ddv2005/AirsoftTracker/data/at.png

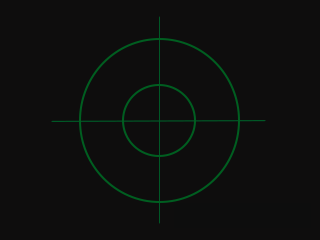
data/at.png
