ddv2005/AirsoftTracker/docs/1.jpg

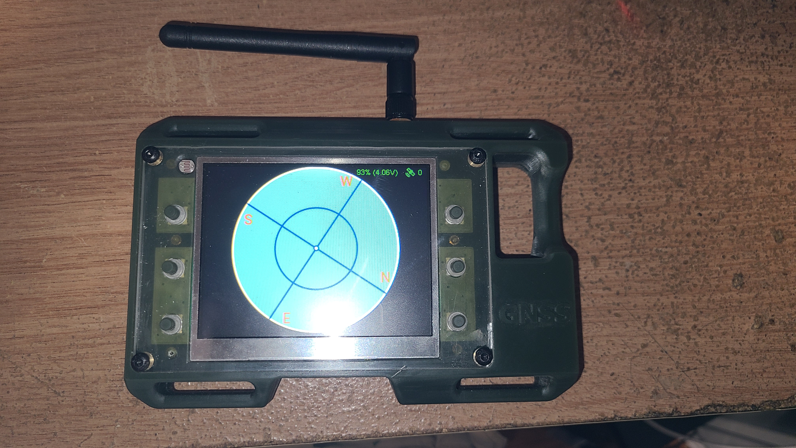
docs/1.jpg
