ddv2005/AirsoftTracker/docs/2.jpg

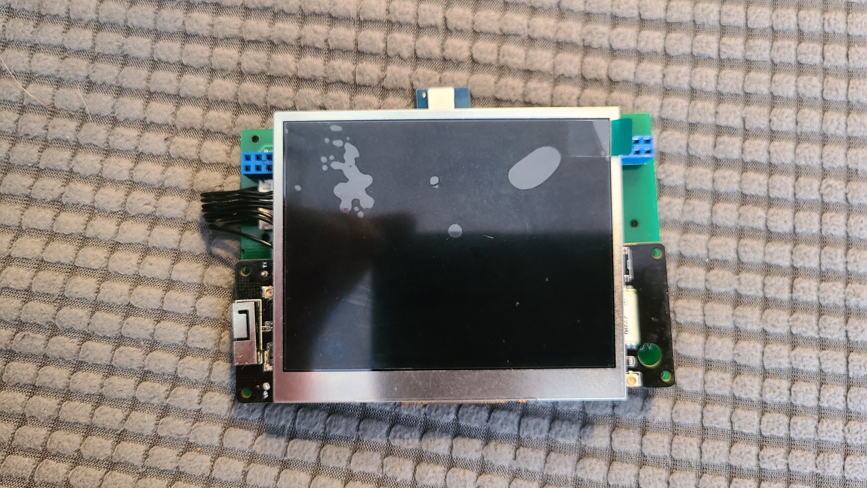
docs/2.jpg
