ddv2005/AirsoftTracker/docs/3.jpg

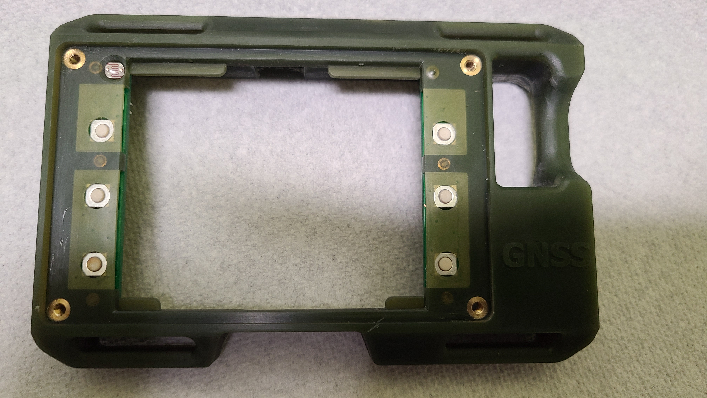
docs/3.jpg
