ddv2005/AirsoftTracker/docs/4.jpg

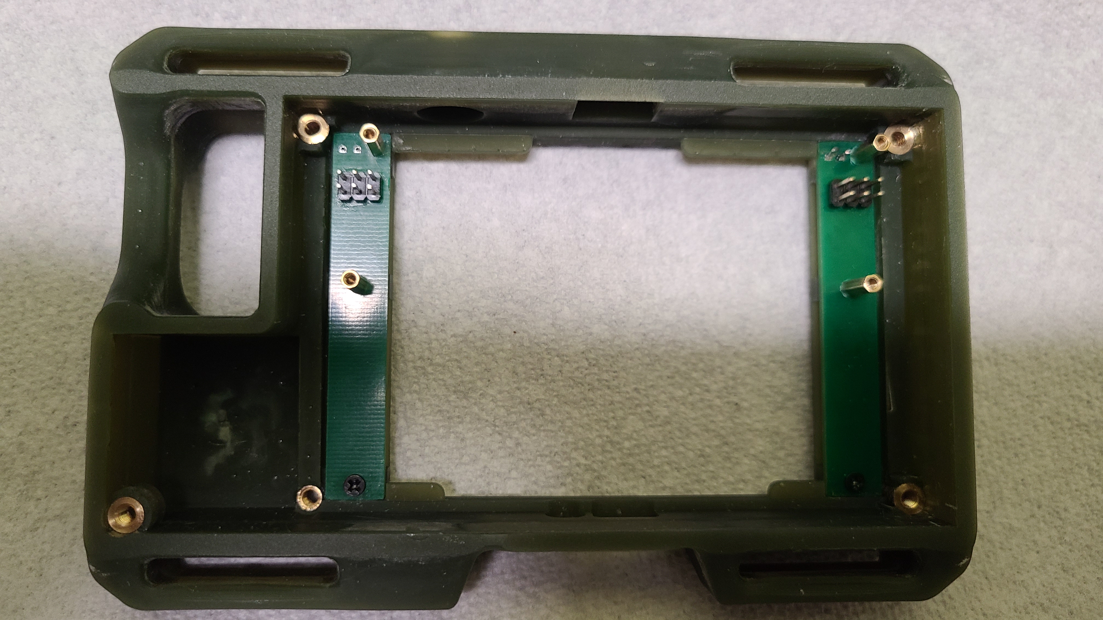
docs/4.jpg
