ddv2005/AirsoftTracker/docs/5.jpg

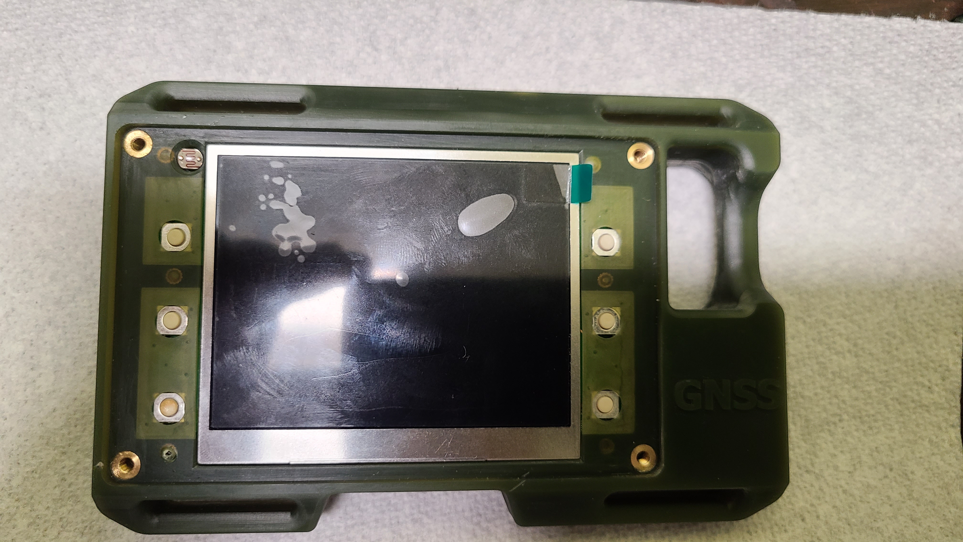
docs/5.jpg
