ddv2005/AirsoftTracker/docs/6.jpg

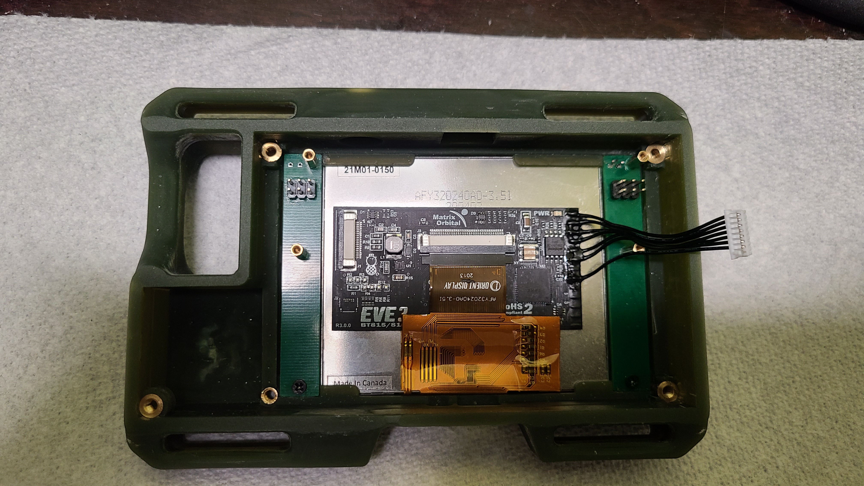
docs/6.jpg
