ddv2005/AirsoftTracker/docs/7.jpg

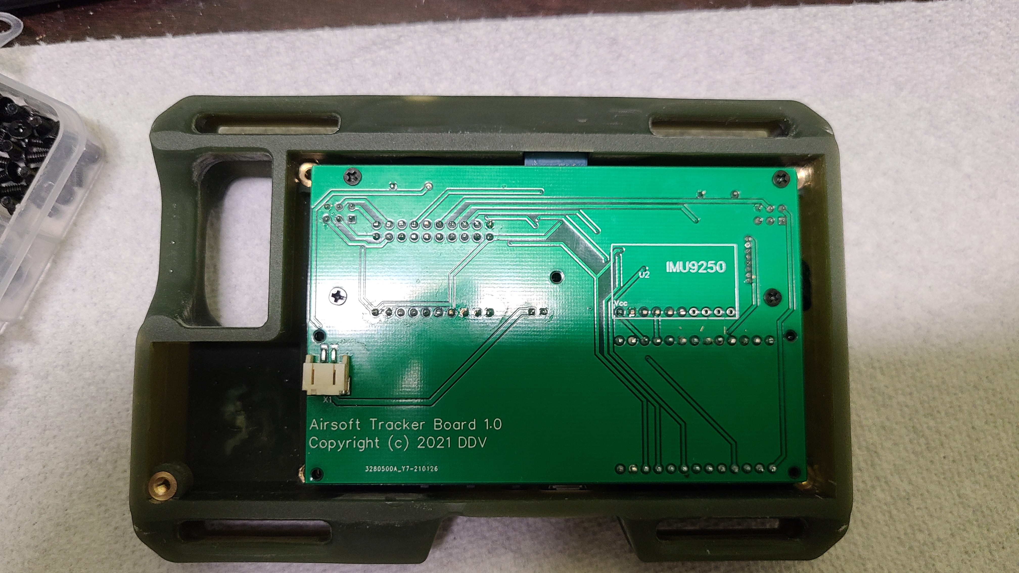
docs/7.jpg
