ddv2005/AirsoftTracker/maps/picasso/tiles/1/0/0.png

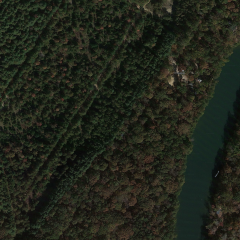
maps/picasso/tiles/1/0/0.png
