ddv2005/AirsoftTracker/maps/picasso/tiles/1/0/1.png

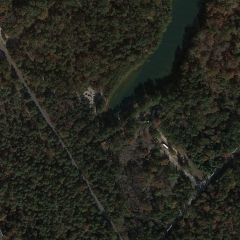
maps/picasso/tiles/1/0/1.png
