ddv2005/AirsoftTracker/maps/picasso/tiles/1/0/2.png

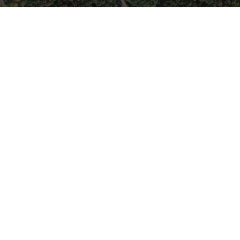
maps/picasso/tiles/1/0/2.png
