ddv2005/AirsoftTracker/maps/picasso/tiles/1/1/0.png

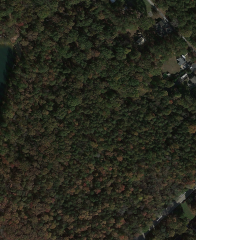
maps/picasso/tiles/1/1/0.png
