ddv2005/AirsoftTracker/maps/picasso/tiles/2/0/4.png

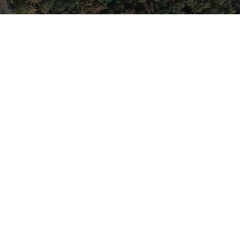
maps/picasso/tiles/2/0/4.png
