ddv2005/AirsoftTracker/maps/picasso/tiles/2/1/1.png

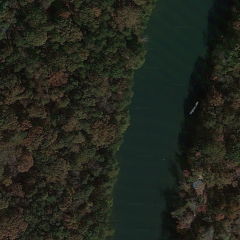
maps/picasso/tiles/2/1/1.png
