ddv2005/AirsoftTracker/maps/picasso/tiles/2/1/2.png

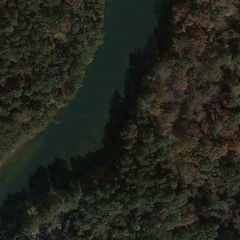
maps/picasso/tiles/2/1/2.png
