ddv2005/AirsoftTracker/maps/picasso/tiles/2/2/0.png

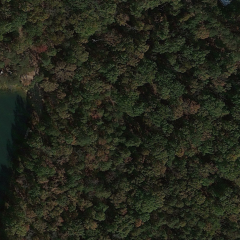
maps/picasso/tiles/2/2/0.png
