ddv2005/AirsoftTracker/maps/picasso/tiles/2/3/1.png

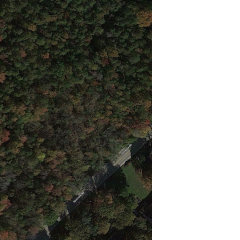
maps/picasso/tiles/2/3/1.png
