ddv2005/AirsoftTracker/maps/picasso/tiles/3/0/4.png

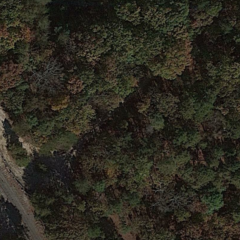
maps/picasso/tiles/3/0/4.png
