ddv2005/AirsoftTracker/maps/picasso/tiles/3/1/7.png

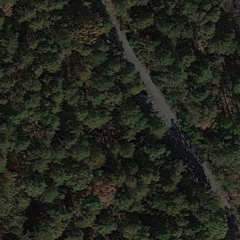
maps/picasso/tiles/3/1/7.png
