ddv2005/AirsoftTracker/maps/picasso/tiles/3/2/1.png

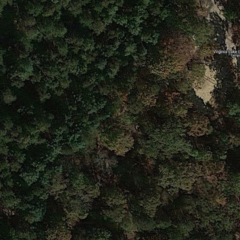
maps/picasso/tiles/3/2/1.png
