ddv2005/AirsoftTracker/maps/picasso/tiles/3/2/3.png

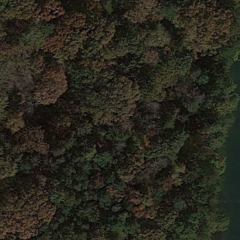
maps/picasso/tiles/3/2/3.png
