ddv2005/AirsoftTracker/maps/picasso/tiles/3/3/4.png

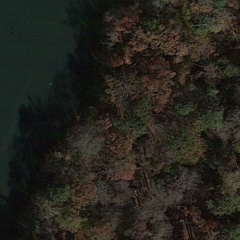
maps/picasso/tiles/3/3/4.png
