ddv2005/AirsoftTracker/maps/picasso/tiles/3/4/0.png

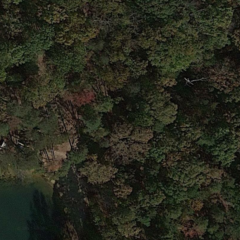
maps/picasso/tiles/3/4/0.png
