ddv2005/AirsoftTracker/maps/picasso/tiles/3/4/6.png

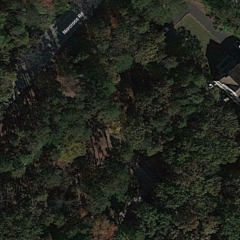
maps/picasso/tiles/3/4/6.png
