ddv2005/AirsoftTracker/maps/picasso/tiles/3/5/0.png

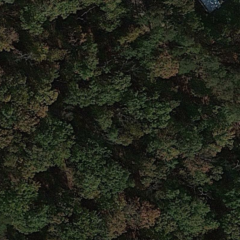
maps/picasso/tiles/3/5/0.png
