ddv2005/AirsoftTracker/maps/picasso/tiles/3/5/1.png

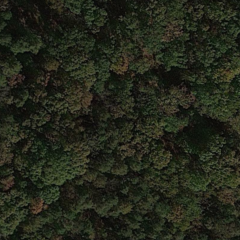
maps/picasso/tiles/3/5/1.png
