ddv2005/AirsoftTracker/maps/picasso/tiles/3/5/4.png

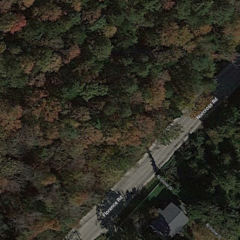
maps/picasso/tiles/3/5/4.png
