ddv2005/AirsoftTracker/maps/picasso/tiles/3/6/5.png

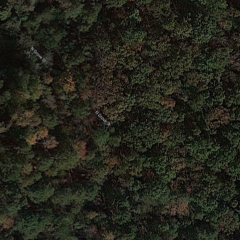
maps/picasso/tiles/3/6/5.png
