ddv2005/AirsoftTracker/maps/picasso/tiles/3/7/2.png

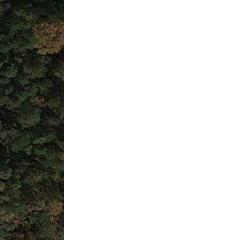
maps/picasso/tiles/3/7/2.png
