ddv2005/AirsoftTracker/maps/picasso/tiles/3/7/5.png

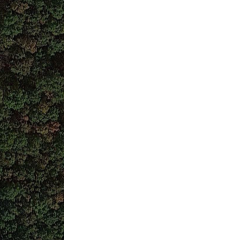
maps/picasso/tiles/3/7/5.png
