ddv2005/AirsoftTracker/maps/zulu24/zulu24/2/2/0.png

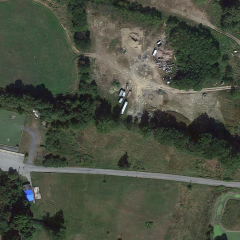
maps/zulu24/zulu24/2/2/0.png
