ddv2005/AirsoftTracker/maps/zulu24/zulu24/2/2/1.png

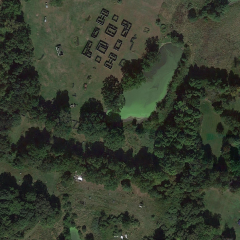
maps/zulu24/zulu24/2/2/1.png
