ddv2005/AirsoftTracker/maps/zulu24/zulu24/2/3/2.png

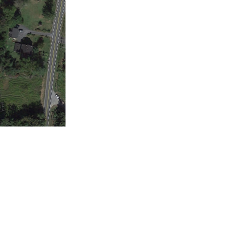
maps/zulu24/zulu24/2/3/2.png
