ddv2005/AirsoftTracker/maps/zulu24/zulu24/3/1/2.png

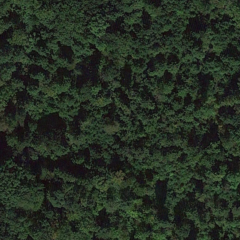
maps/zulu24/zulu24/3/1/2.png
