ddv2005/AirsoftTracker/maps/zulu24/zulu24/3/3/1.png

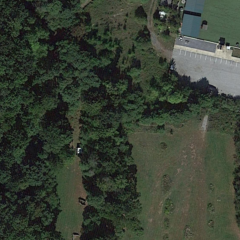
maps/zulu24/zulu24/3/3/1.png
