ddv2005/AirsoftTracker/maps/zulu24/zulu24/3/4/3.png

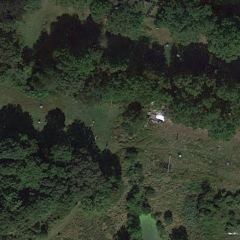
maps/zulu24/zulu24/3/4/3.png
