ddv2005/AirsoftTracker/screens/mainscreen/resources/Untitled-2.jpg

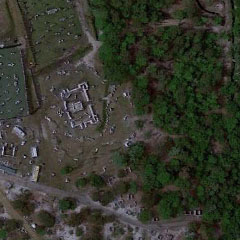
screens/mainscreen/resources/Untitled-2.jpg
