ddv2005/AirsoftTracker/src/atstrings.h

#pragma once

#include <pgmspace.h>

#define ATS_DEAD PSTR("DEAD")
#define ATS_ALIVE PSTR("ALIVE")
#define ATS_BTN_DEAD PSTR("[L]->DEAD")
#define ATS_BTN_ALIVE PSTR("[L]->ALIVE")
#define ATS_MENU PSTR("MENU")
#define ATS_MRADIUS PSTR("RADIUS/MAP")
